bjohan/lmx2594/py/default_config.py

conf = {112: 0, 111: 0, 110: 0, 109: 0, 108: 0, 107: 0, 106: 0, 105: 33, 104: 0, 103: 0, 102: 0, 101: 17, 100: 0, 99: 0, 98: 0, 97: 2184, 96: 0, 95: 0, 94: 0, 93: 0, 92: 0, 91: 0, 90: 0, 89: 0, 88: 0, 87: 0, 86: 0, 85: 0, 84: 0, 83: 0, 82: 0, 81: 0, 80: 0, 79: 0, 78: 3, 77: 0, 76: 12, 75: 2048, 74: 0, 73: 63, 72: 1, 71: 129, 70: 50000, 69: 0, 68: 1000, 67: 0, 66: 500, 65: 0, 64: 5000, 63: 0, 62: 802, 61: 168, 60: 0, 59: 1, 58: 36865, 57: 32, 56: 0, 55: 0, 54: 0, 53: 0, 52: 2080, 51: 128, 50: 0, 49: 16768, 48: 768, 47: 768, 46: 2045, 45: 51423, 44: 8099, 43: 0, 42: 0, 41: 0, 40: 0, 39: 1000, 38: 0, 37: 1028, 36: 63, 35: 4, 34: 0, 33: 7713, 32: 915, 31: 17388, 30: 12684, 29: 12684, 28: 1160, 27: 2, 26: 3504, 25: 3115, 24: 1818, 23: 124, 22: 1, 21: 1025, 20: 57416, 19: 10167, 18: 100, 17: 300, 16: 128, 15: 1615, 14: 7792, 13: 16384, 12: 20484, 11: 24, 10: 4312, 9: 5636, 8: 8192, 7: 16562, 6: 51202, 5: 200, 4: 6211, 3: 1602, 2: 1280, 1: 2056, 0: 9500}
